jackw01/glowstick/img/DSCF6181.jpg

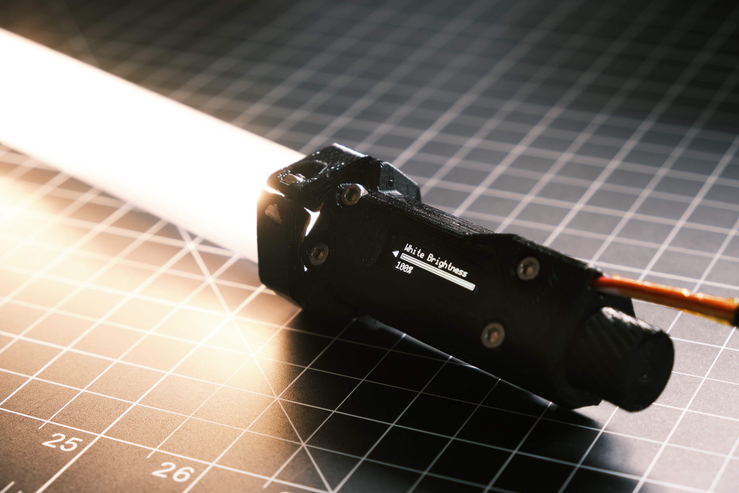
img/DSCF6181.jpg
