jackw01/glowstick/img/DSCF6184.jpg

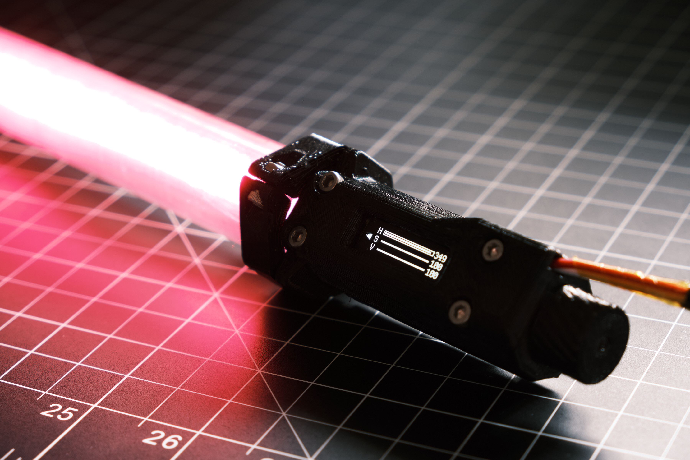
img/DSCF6184.jpg
